worxbend/twitch-screen/twitch-screen-cad-design/output/preview/03_side.png

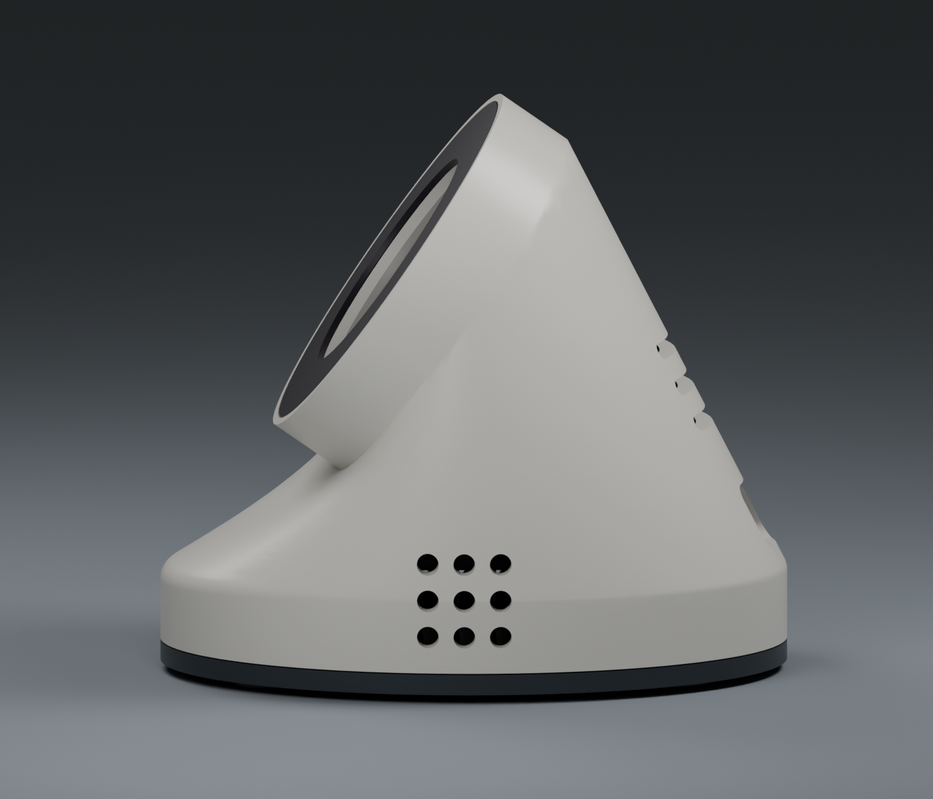
twitch-screen-cad-design/output/preview/03_side.png
