worxbend/twitch-screen/twitch-screen-cad-design/output/preview/part_base.png

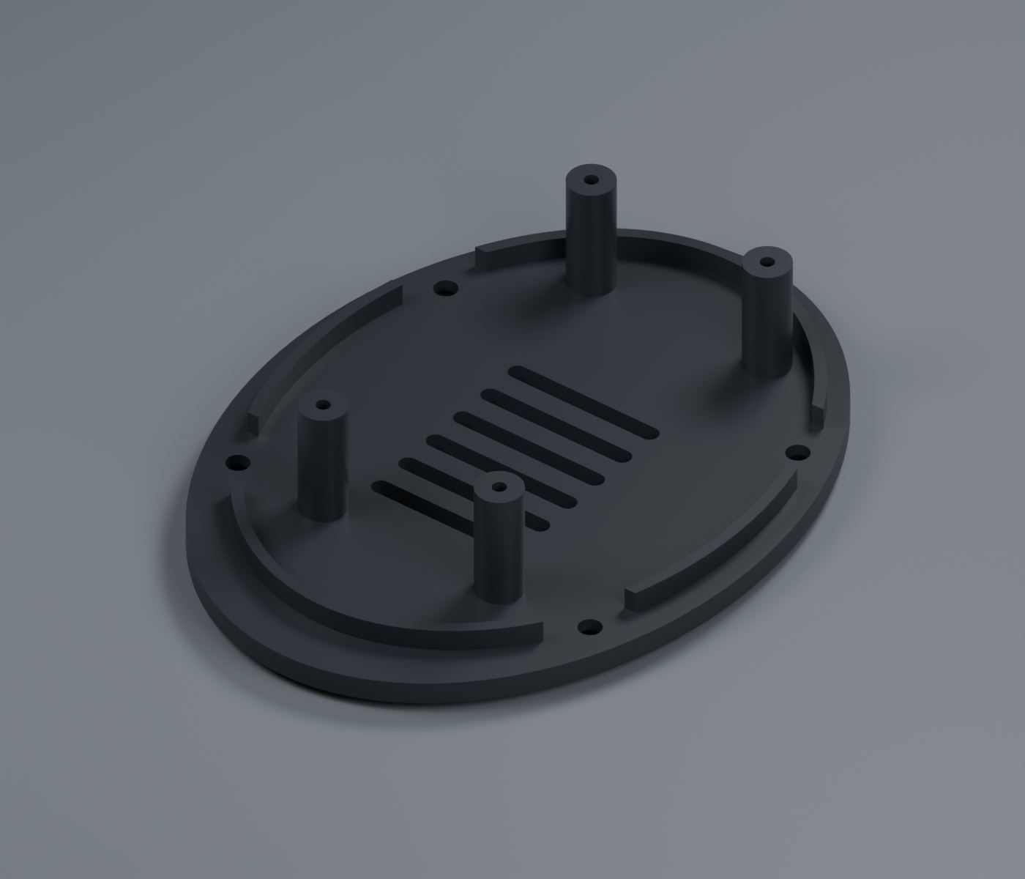
twitch-screen-cad-design/output/preview/part_base.png
