worxbend/twitch-screen/twitch-screen-cad-design/output/preview/part_face_bezel.png

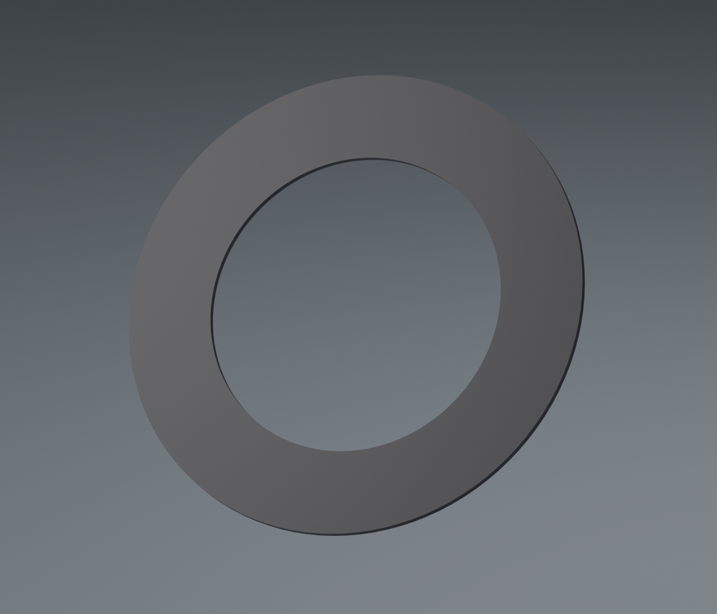
twitch-screen-cad-design/output/preview/part_face_bezel.png
