worxbend/twitch-screen/twitch-screen-cad-design/output/preview/part_lcd_retainer.png

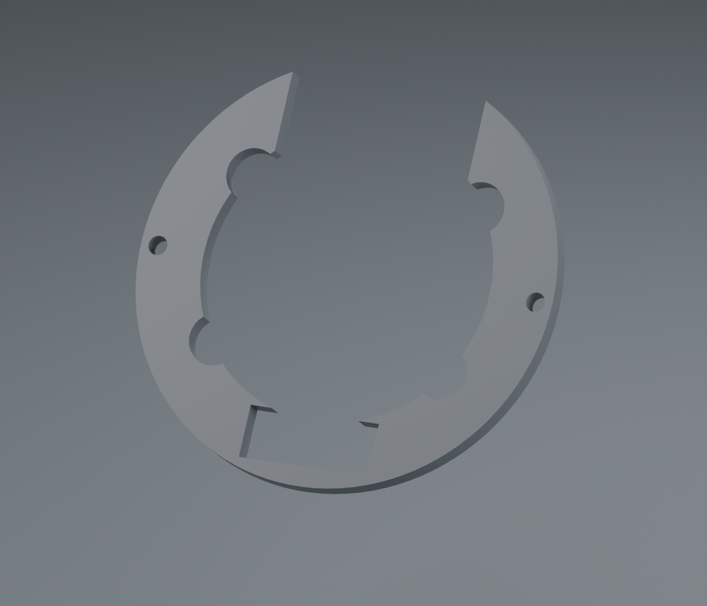
twitch-screen-cad-design/output/preview/part_lcd_retainer.png
