worxbend/twitch-screen/twitch-screen-cad-design/output/preview/part_shell_interior.png

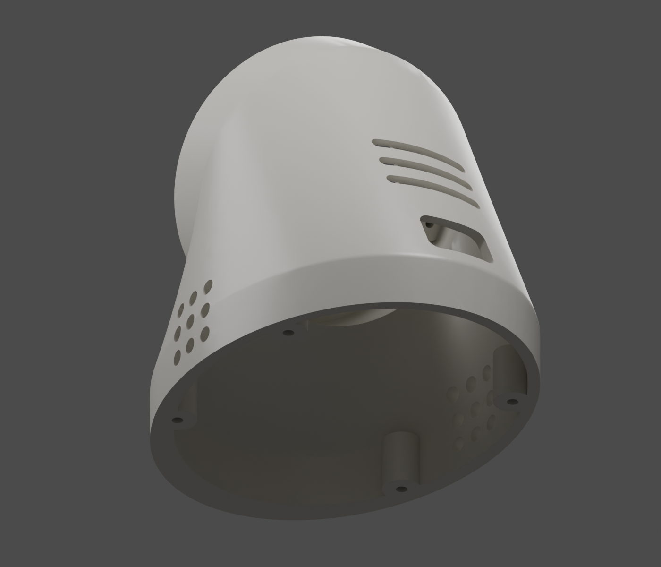
twitch-screen-cad-design/output/preview/part_shell_interior.png
