worxbend/twitch-screen/twitch-screen-cad-design/refs/datasheets/waveshare_rear.jpg

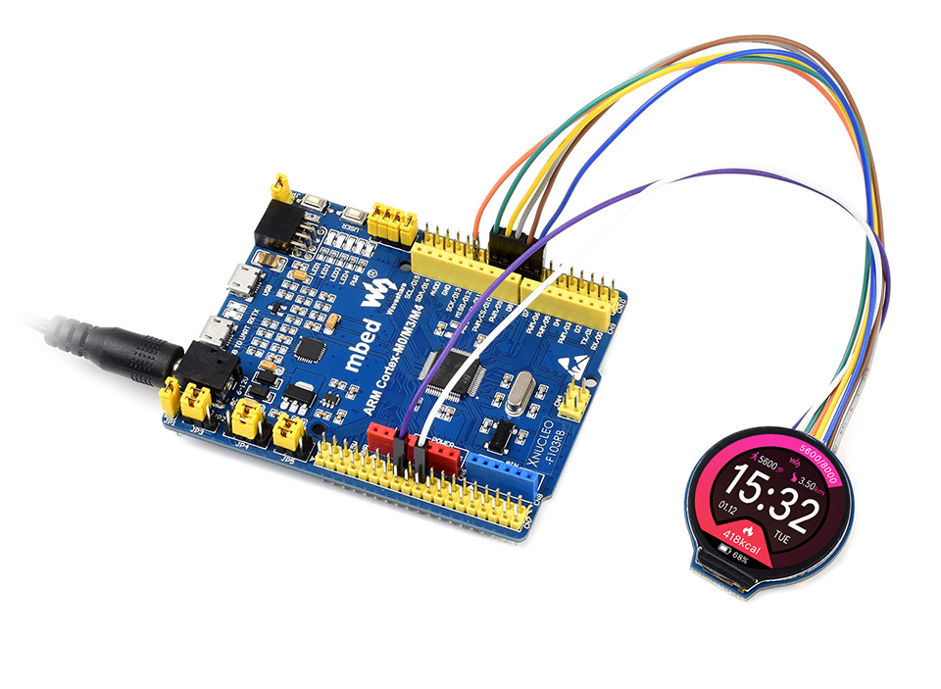
twitch-screen-cad-design/refs/datasheets/waveshare_rear.jpg
