worxbend/twitch-screen/twitch-screen-cad-design/refs/hardware/1000011987.jpg

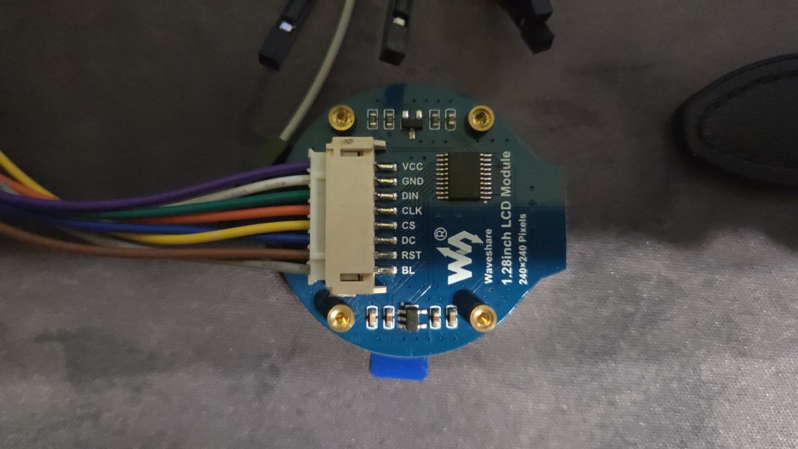
twitch-screen-cad-design/refs/hardware/1000011987.jpg
