worxbend/twitch-screen/twitch-screen-cad-design/output/render_meshes/usb_socket.stl

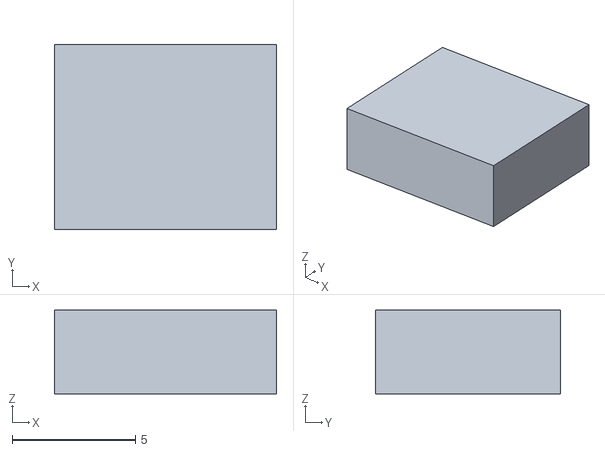
[picture p42: CAD file, 2026-09-25]
twitch-screen-cad-design/output/render_meshes/usb_socket.stl
9.00 x 7.50 x 3.40
