worxbend/twitch-screen/twitch-screen-cad-design/output/render_meshes/esp32_shield.stl

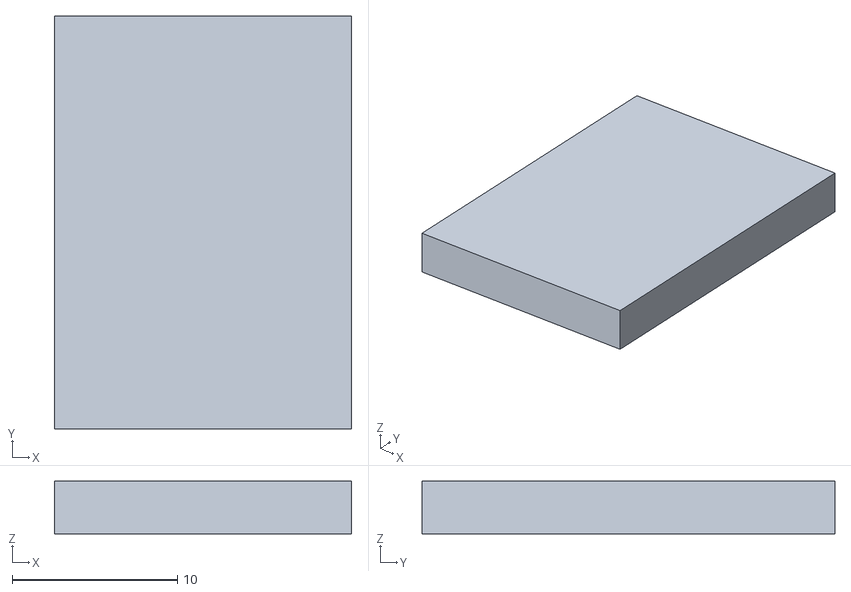
[picture p43: CAD file, 2026-09-25]
twitch-screen-cad-design/output/render_meshes/esp32_shield.stl
18.0 x 25.0 x 3.20
