worxbend/twitch-screen/twitch-screen-cad-design/output/render_meshes/face_bezel.stl

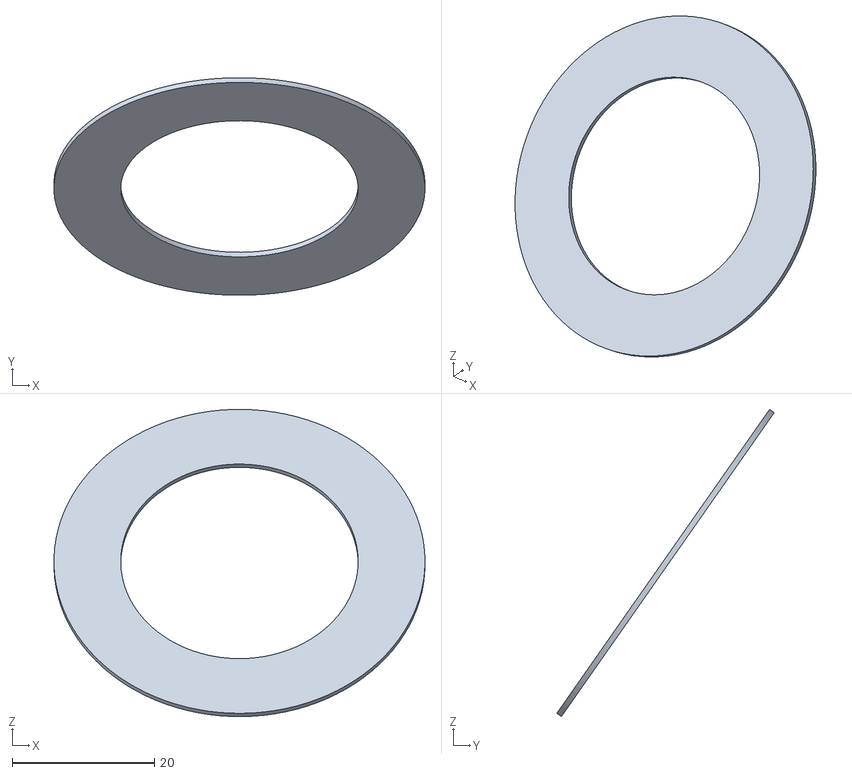
[picture p44: CAD file, 2026-09-25]
twitch-screen-cad-design/output/render_meshes/face_bezel.stl
52.2 x 30.6 x 43.2
