worxbend/twitch-screen/twitch-screen-cad-design/output/render_meshes/lcd_connector.stl

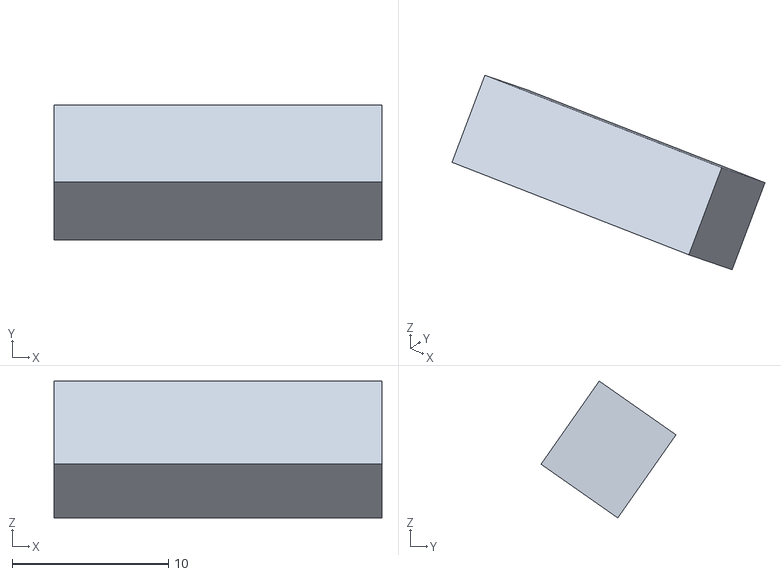
[picture p45: CAD file, 2026-09-25]
twitch-screen-cad-design/output/render_meshes/lcd_connector.stl
21.0 x 8.64 x 8.77
