worxbend/twitch-screen/twitch-screen-cad-design/output/render_meshes/cable_route.stl

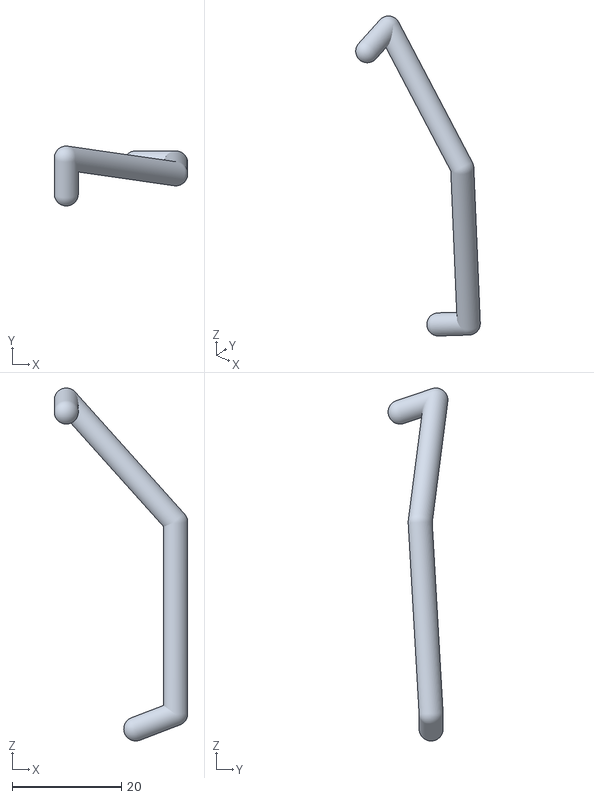
[picture p46: CAD file, 2026-09-25]
twitch-screen-cad-design/output/render_meshes/cable_route.stl
24.4 x 10.9 x 64.5
