worxbend/twitch-screen/twitch-screen-cad-design/output/render_meshes/buttons.stl

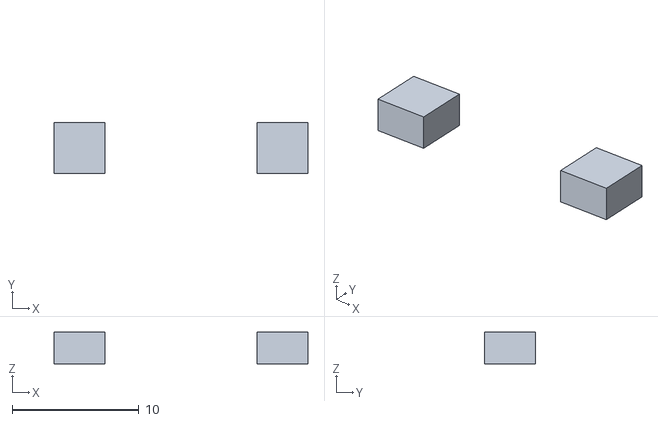
[picture p47: CAD file, 2026-09-25]
twitch-screen-cad-design/output/render_meshes/buttons.stl
20.0 x 4.00 x 2.50
