worxbend/twitch-screen/twitch-screen-firmware/src/ui_idle.cpp

#include "ui_idle.h"

#include <Arduino.h>
#include <array>
#include <lvgl.h>

#include "assets/twitch_glitch.h"
#include "presentation.h"
#include "stats_render_plan.h"
#include "ui_common.h"

// Layout for the 240x240 round panel (radius 120, center 120,120).
// Usable half-width at offset y from center: sqrt(120^2 - y^2) minus ~8 px
// of bezel/gauge margin. Everything below is placed to respect that curve:
//   y=62 -> ~94 px, y=80 -> ~81 px, y=90 -> ~71 px.
// The edge gauge is an arc of outer radius 117 and width 3, so nothing may
// reach past r = 114; the bottom chip row is placed at r_max = 109.

namespace {

constexpr uint32_t COUNT_ANIM_MS = 800;
// Viewer counts at or above this skip the count-up animation and are drawn
// directly; formatCount shows them as whole thousands or more ("10K" and up).
constexpr uint32_t VIEWER_ANIM_MAX = 10000;

const lv_color_t COL_BG = lv_color_hex(0x0E0E10);
const lv_color_t COL_PURPLE = lv_color_hex(0x9146FF);
const lv_color_t COL_TRACK = lv_color_hex(0x1F1F23);
const lv_color_t COL_TEXT = lv_color_hex(0xEFEFF1);
const lv_color_t COL_DIM = lv_color_hex(0x7A7A88);
const lv_color_t COL_LIVE = lv_color_hex(0xEB0400);

lv_obj_t *liveGroup = nullptr;
lv_obj_t *offlineGroup = nullptr;

lv_obj_t *edgeArc = nullptr;
lv_obj_t *liveDot = nullptr;
lv_obj_t *uptimeLabel = nullptr;
lv_obj_t *viewersValue = nullptr;
lv_obj_t *chipChat = nullptr;
lv_obj_t *chipFoll = nullptr;
lv_obj_t *chipSubs = nullptr;
// §6.5's "the last value stays on screen until the next stream begins": the same
// three totals, on the offline screen, because that is where they have to survive.
lv_obj_t *offChipChat = nullptr;
lv_obj_t *offChipFoll = nullptr;
lv_obj_t *offChipSubs = nullptr;
lv_obj_t *connectGroup = nullptr;
lv_obj_t *connLabel = nullptr;

// The three inputs that decide which screen is up (visibleStatsGroup).
struct ScreenState {
  bool linkUp = false;
  bool covered = false;
  bool live = false;
};
ScreenState screen;
lv_timer_t *dotsTimer = nullptr;
lv_timer_t *uptimeTimer = nullptr;
lv_obj_t *connectSpinner = nullptr;
lv_obj_t *connectLogo = nullptr;
StreamStats latestStats;
char viewersText[8] = {};
char uptimeText[16] = {};

static_assert(sizeof(twitch_glitch_48) == 48u * 48u * sizeof(uint16_t), "48px asset size");
static_assert(sizeof(twitch_glitch_84) == 84u * 84u * sizeof(uint16_t), "84px asset size");

lv_image_dsc_t glitch48;
lv_image_dsc_t glitch84;

// What the panel shows; every STATS is planned against it (stats_render_plan.h).
StatsShown shown;

// §6.5 local uptime ticking. uptime_s is a snapshot taken at server_time and
// STATS only arrives every 5 s, so the label would step in 5 s jumps. Anchor
// the value against millis() on receipt and re-anchor on every STATS, which
// makes it tick once a second without ever drifting away from the relay.
struct UptimeClock {
  uint32_t base = 0;
  uint32_t anchorMs = 0;
  bool valid = false;
};
UptimeClock uptime;

void initDsc(lv_image_dsc_t *d, const uint16_t *data, int size) {
  memset(d, 0, sizeof(*d));
#ifdef LV_IMAGE_HEADER_MAGIC
  d->header.magic = LV_IMAGE_HEADER_MAGIC;
#endif
  d->header.cf = LV_COLOR_FORMAT_RGB565;
  d->header.w = size;
  d->header.h = size;
  d->header.stride = size * 2;
  d->data_size = size * size * 2;
  d->data = (const uint8_t *)data;
}

lv_obj_t *makeLabelAt(lv_obj_t *parent, const lv_font_t *font, lv_color_t color,
                      lv_align_t align, int x, int y) {
  lv_obj_t *l = lv_label_create(parent);
  lv_obj_set_style_text_font(l, font, 0);
  lv_obj_set_style_text_color(l, color, 0);
  lv_obj_align(l, align, x, y);
  return l;
}

lv_obj_t *makeLabel(lv_obj_t *parent, const lv_font_t *font, lv_color_t color,
                    lv_align_t align, int y) {
  return makeLabelAt(parent, font, color, align, 0, y);
}

void pulseAnim(void *var, int32_t v) {
  lv_obj_set_style_opa(static_cast<lv_obj_t *>(var), static_cast<lv_opa_t>(v), 0);
}

void startPulse(lv_obj_t *obj, lv_opa_t lo, lv_opa_t hi, uint32_t ms) {
  lv_anim_t a;
  lv_anim_init(&a);
  lv_anim_set_var(&a, obj);
  lv_anim_set_values(&a, lo, hi);
  lv_anim_set_duration(&a, ms);
  lv_anim_set_exec_cb(&a, pulseAnim);
  lv_anim_set_path_cb(&a, lv_anim_path_ease_in_out);
  lv_anim_set_repeat_count(&a, LV_ANIM_REPEAT_INFINITE);
  lv_anim_set_reverse_duration(&a, ms);
  lv_anim_start(&a);
}

void viewersAnim(void *var, int32_t v) {
  std::array<char, sizeof(viewersText)> text;
  formatCount(text.data(), text.size(), v < 0 ? 0u : (uint32_t)v);
  setStaticLabel(static_cast<lv_obj_t *>(var), viewersText, text.data());
}

// `from` is the previously shown value (-1 = unknown), the count-up origin.
void setViewers(int64_t from, uint32_t v) {
  lv_anim_delete(viewersValue, viewersAnim);
  if (v >= VIEWER_ANIM_MAX) {
    std::array<char, sizeof(viewersText)> text;
    formatCount(text.data(), text.size(), v);
    setStaticLabel(viewersValue, viewersText, text.data());
    return;
  }
  lv_anim_t a;
  lv_anim_init(&a);
  lv_anim_set_var(&a, viewersValue);
  lv_anim_set_values(&a, from < 0 || from >= (int64_t)VIEWER_ANIM_MAX ? (int32_t)v : (int32_t)from, (int32_t)v);
  lv_anim_set_duration(&a, COUNT_ANIM_MS);
  lv_anim_set_exec_cb(&a, viewersAnim);
  lv_anim_set_path_cb(&a, lv_anim_path_ease_out);
  lv_anim_start(&a);
}

void formatUptime(char *buf, size_t n, uint32_t sec) {
  snprintf(buf, n, "%lu:%02lu:%02lu", (unsigned long)(sec / 3600),
           (unsigned long)(sec / 60 % 60), (unsigned long)(sec % 60));
}

void renderUptime() {
  if (!uptime.valid) return;
  const uint32_t sec = uptime.base + (millis() - uptime.anchorMs) / 1000;
  std::array<char, sizeof(uptimeText)> buf;
  formatUptime(buf.data(), buf.size(), sec);
  setStaticLabel(uptimeLabel, uptimeText, buf.data());
}

void uptimeTickCb(lv_timer_t *) {
  if (!screen.live || !screen.linkUp || screen.covered) return;
  renderUptime();
}

// Bottom stat row: the three numbers that matter while live, plus the two the
// relay has always sent and the v2 screen threw away (STATS +12 followers,
// +16 subs). Values at y=62, captions at y=80, x = -50 / 0 / +50 — the far
// corner of the outermost caption sits at r = 109, inside the edge gauge.
lv_obj_t *makeChip(lv_obj_t *parent, int x, const char *caption) {
  lv_obj_t *value = makeLabelAt(parent, &lv_font_montserrat_14, COL_TEXT,
                                LV_ALIGN_CENTER, x, 62);
  lv_label_set_text_static(value, "0");
  lv_obj_t *cap = makeLabelAt(parent, &lv_font_montserrat_14, COL_DIM,
                              LV_ALIGN_CENTER, x, 80);
  lv_obj_set_style_text_letter_space(cap, 1, 0);
  lv_label_set_text_static(cap, caption);
  return value;
}

void buildLive(lv_obj_t *scr) {
  liveGroup = lv_obj_create(scr);
  lv_obj_set_size(liveGroup, PANEL, PANEL);
  lv_obj_center(liveGroup);
  lv_obj_set_style_bg_opa(liveGroup, LV_OPA_TRANSP, 0);
  lv_obj_set_style_pad_all(liveGroup, 0, 0);
  clearDecor(liveGroup);

  // Full-ring chat-activity gauge hugging the round edge.
  edgeArc = lv_arc_create(liveGroup);
  lv_obj_set_size(edgeArc, 234, 234);
  lv_obj_center(edgeArc);
  lv_arc_set_rotation(edgeArc, 270);
  lv_arc_set_bg_angles(edgeArc, 0, 360);
  lv_arc_set_range(edgeArc, 0, 100);
  lv_arc_set_value(edgeArc, 0);
  lv_obj_set_style_arc_width(edgeArc, 3, LV_PART_MAIN);
  lv_obj_set_style_arc_width(edgeArc, 3, LV_PART_INDICATOR);
  lv_obj_set_style_arc_color(edgeArc, COL_TRACK, LV_PART_MAIN);
  lv_obj_set_style_arc_color(edgeArc, COL_PURPLE, LV_PART_INDICATOR);
  lv_obj_set_style_arc_rounded(edgeArc, true, LV_PART_INDICATOR);
  lv_obj_remove_style(edgeArc, nullptr, LV_PART_KNOB);
  lv_obj_set_clickable(edgeArc, false);

  // LIVE pill.
  lv_obj_t *pill = lv_obj_create(liveGroup);
  lv_obj_set_size(pill, 62, 20);
  lv_obj_align(pill, LV_ALIGN_CENTER, 0, -90);
  lv_obj_set_style_bg_color(pill, COL_LIVE, 0);
  lv_obj_set_style_radius(pill, 10, 0);
  lv_obj_set_style_pad_all(pill, 0, 0);
  clearDecor(pill);

  liveDot = lv_obj_create(pill);
  lv_obj_set_size(liveDot, 7, 7);
  lv_obj_align(liveDot, LV_ALIGN_LEFT_MID, 10, 0);
  lv_obj_set_style_bg_color(liveDot, lv_color_white(), 0);
  lv_obj_set_style_radius(liveDot, LV_RADIUS_CIRCLE, 0);
  clearDecor(liveDot);

  lv_obj_t *liveTxt = makeLabel(pill, &lv_font_montserrat_14,
                                lv_color_white(), LV_ALIGN_LEFT_MID, 0);
  lv_obj_set_x(liveTxt, 22);
  lv_label_set_text_static(liveTxt, "LIVE");

  // Time since stream start — one of the three numbers the screen exists for.
  uptimeLabel = makeLabel(liveGroup, &lv_font_montserrat_14, COL_DIM,
                          LV_ALIGN_CENTER, -70);
  lv_label_set_text_static(uptimeLabel, "0:00:00");
  uptimeTimer = lv_timer_create(uptimeTickCb, 1000, nullptr);

  lv_obj_t *logo = lv_image_create(liveGroup);
  lv_image_set_src(logo, &glitch48);
  lv_obj_align(logo, LV_ALIGN_CENTER, 0, -32);

  viewersValue = makeLabel(liveGroup, &lv_font_montserrat_48, COL_TEXT,
                           LV_ALIGN_CENTER, 8);
  lv_label_set_text_static(viewersValue, "0");

  lv_obj_t *caption = makeLabel(liveGroup, &lv_font_montserrat_14, COL_DIM,
                                LV_ALIGN_CENTER, 44);
  lv_obj_set_style_text_letter_space(caption, 2, 0);
  lv_label_set_text_static(caption, "VIEWERS");

  chipFoll = makeChip(liveGroup, -50, "FLW");
  chipChat = makeChip(liveGroup, 0, "MSG");
  chipSubs = makeChip(liveGroup, 50, "SUB");
}

void buildOffline(lv_obj_t *scr) {
  offlineGroup = lv_obj_create(scr);
  lv_obj_set_size(offlineGroup, PANEL, PANEL);
  lv_obj_center(offlineGroup);
  lv_obj_set_style_bg_opa(offlineGroup, LV_OPA_TRANSP, 0);
  lv_obj_set_style_pad_all(offlineGroup, 0, 0);
  clearDecor(offlineGroup);

  // Everything moves up to make room for the stat row at the same y as the live
  // screen's (values 62, captions 80), so the two screens do not shuffle the
  // numbers around when a stream ends. The 84 px logo centred at -52 spans
  // -94..-10, clear of OFFLINE at 8 and of the round bezel at r = 114.
  lv_obj_t *logo = lv_image_create(offlineGroup);
  lv_image_set_src(logo, &glitch84);
  lv_obj_set_style_opa(logo, 70, 0);
  lv_obj_align(logo, LV_ALIGN_CENTER, 0, -52);

  lv_obj_t *off = makeLabel(offlineGroup, &lv_font_montserrat_28, COL_DIM,
                            LV_ALIGN_CENTER, 8);
  lv_obj_set_style_text_letter_space(off, 2, 0);
  lv_label_set_text_static(off, "OFFLINE");

  lv_obj_t *sub = makeLabel(offlineGroup, &lv_font_montserrat_14, COL_DIM,
                            LV_ALIGN_CENTER, 34);
  lv_label_set_text_static(sub, "waiting to go live");

  offChipFoll = makeChip(offlineGroup, -50, "FLW");
  offChipChat = makeChip(offlineGroup, 0, "MSG");
  offChipSubs = makeChip(offlineGroup, 50, "SUB");

  lv_obj_set_hidden(offlineGroup, true);
}

lv_obj_t *makeGroup(lv_obj_t *scr) {
  lv_obj_t *g = lv_obj_create(scr);
  lv_obj_set_size(g, PANEL, PANEL);
  lv_obj_center(g);
  lv_obj_set_style_bg_opa(g, LV_OPA_TRANSP, 0);
  lv_obj_set_style_pad_all(g, 0, 0);
  clearDecor(g);
  return g;
}

void spinAnim(void *var, int32_t v) {
  lv_arc_set_rotation(static_cast<lv_obj_t *>(var), v);
}

void dotsCb(lv_timer_t *) {
  static const std::array<const char *, 4> labels = {
      {"CONNECTING", "CONNECTING.", "CONNECTING..", "CONNECTING..."}};
  static size_t n = 0;
  n = (n + 1) % labels.size();
  lv_label_set_text_static(connLabel, labels[n]);
}

void buildConnect(lv_obj_t *scr) {
  connectGroup = makeGroup(scr);

  // Purple spinner arc orbiting the logo.
  lv_obj_t *spinner = connectSpinner = lv_arc_create(connectGroup);
  lv_obj_set_size(spinner, 140, 140);
  lv_obj_align(spinner, LV_ALIGN_CENTER, 0, -14);
  lv_arc_set_bg_angles(spinner, 0, 80);
  lv_arc_set_range(spinner, 0, 100);
  lv_arc_set_value(spinner, 100);
  lv_obj_set_style_arc_width(spinner, 5, LV_PART_MAIN);
  lv_obj_set_style_arc_width(spinner, 5, LV_PART_INDICATOR);
  lv_obj_set_style_arc_color(spinner, COL_TRACK, LV_PART_MAIN);
  lv_obj_set_style_arc_color(spinner, COL_PURPLE, LV_PART_INDICATOR);
  lv_obj_set_style_arc_rounded(spinner, true, LV_PART_INDICATOR);
  lv_obj_remove_style(spinner, nullptr, LV_PART_KNOB);
  lv_obj_set_clickable(spinner, false);

  lv_obj_t *logo = connectLogo = lv_image_create(connectGroup);
  lv_image_set_src(logo, &glitch84);
  lv_obj_align(logo, LV_ALIGN_CENTER, 0, -14);

  connLabel = makeLabel(connectGroup, &lv_font_montserrat_20, COL_DIM,
                        LV_ALIGN_CENTER, 72);
  lv_label_set_text_static(connLabel, "CONNECTING");
  dotsTimer = lv_timer_create(dotsCb, 450, nullptr);
}

// Applies the plan for the cached STATS: only the visible group, only the
// fields whose shown text or value changed.
void renderVisibleStats() {
  const StatsRenderPlan plan = planStatsRender(shown, latestStats, screen.linkUp, screen.covered);
  if (plan.group == StatsGroup::None) return;
  const bool live = plan.group == StatsGroup::Live;
  const int64_t previousViewers = shown.viewers;
  // Commit first: the chips then point at the mirror's own storage.
  commitStatsPlan(shown, plan);
  const ChipTexts &texts = live ? shown.live : shown.offline;
  if (plan.chat) lv_label_set_text_static(live ? chipChat : offChipChat, texts.chat);
  if (plan.foll) lv_label_set_text_static(live ? chipFoll : offChipFoll, texts.foll);
  if (plan.subs) lv_label_set_text_static(live ? chipSubs : offChipSubs, texts.subs);
  if (plan.uptime) renderUptime();
  if (plan.viewers) setViewers(previousViewers, plan.viewersValue);
  if (plan.arc) lv_arc_set_value(edgeArc, plan.arcValue);
}

void startSpinner() {
  lv_anim_t a;
  lv_anim_init(&a);
  lv_anim_set_var(&a, connectSpinner);
  lv_anim_set_values(&a, 0, 360);
  lv_anim_set_duration(&a, 1400);
  lv_anim_set_exec_cb(&a, spinAnim);
  lv_anim_set_repeat_count(&a, LV_ANIM_REPEAT_INFINITE);
  lv_anim_start(&a);

}

void applyVisibility() {
  const StatsGroup group = visibleStatsGroup(screen.linkUp, screen.covered, screen.live);
  const bool connecting = !screen.covered && !screen.linkUp;
  const bool live = group == StatsGroup::Live;
  lv_obj_set_hidden(connectGroup, !connecting);
  lv_obj_set_hidden(liveGroup, !live);
  lv_obj_set_hidden(offlineGroup, group != StatsGroup::Offline);
  lv_timer_pause(dotsTimer);
  lv_timer_pause(uptimeTimer);
  lv_anim_delete(connectSpinner, spinAnim);
  lv_anim_delete(connectLogo, pulseAnim);
  lv_anim_delete(liveDot, pulseAnim);
  if (connecting) {
    lv_timer_resume(dotsTimer);
    startSpinner();
    startPulse(connectLogo, 110, 255, 1200);
  }
  if (live) {
    lv_timer_resume(uptimeTimer);
    startPulse(liveDot, 255, 60, 700);
  } else {
    lv_anim_delete(viewersValue, viewersAnim);
    forgetLiveViewers(shown);
  }
  renderVisibleStats();
}

}  // namespace

void uiIdleBuild() {
  initDsc(&glitch48, twitch_glitch_48, 48);
  initDsc(&glitch84, twitch_glitch_84, 84);

  lv_obj_t *scr = lv_screen_active();
  lv_obj_set_style_bg_color(scr, COL_BG, 0);

  buildLive(scr);
  buildOffline(scr);
  buildConnect(scr);
  initStatsShown(shown);
  applyVisibility();  // starts in CONNECTING state until the link is up
}

void uiIdleSetStats(const StreamStats &s) {
  latestStats = s;
  const bool changed = screen.live != (s.live != 0);
  screen.live = s.live != 0;
  uptime.valid = screen.live;
  uptime.base = (s.streamStartedAt != 0 && s.serverTime >= s.streamStartedAt)
                    ? (s.serverTime - s.streamStartedAt) : s.uptimeSec;
  uptime.anchorMs = millis();
  if (changed) applyVisibility();
  else renderVisibleStats();
}

void uiIdleSetOnline(bool online) {
  if (!connectGroup || online == screen.linkUp) return;
  screen.linkUp = online;
  applyVisibility();
}

void uiIdleSetCovered(bool value) {
  if (!connectGroup || screen.covered == value) return;
  screen.covered = value;
  applyVisibility();
}
