worxbend/twitch-screen/twitch-screen-firmware/src/credentials.example.h

// Copy this file to credentials.h and fill in real values.
// credentials.h is git-ignored and must never be committed.
#pragma once

#define WIFI_SSID "your-ssid"
#define WIFI_PASSWORD "your-password"

// Notification server, protocol TSB/3 (persistent TCP binary, docs/PROTOCOL.md).
#define SERVER_HOST "192.168.1.100"
#define SERVER_PORT 8099

// Empty selects lcd-<chip MAC>, unique per physical device. Set a unique custom
// name only if needed; duplicate names cause relay REPLACED disconnects.
#define DEVICE_ID ""
